grodansparadis/vscp-p1-pulse-interface/images/IMG_20221014_143849.jpg

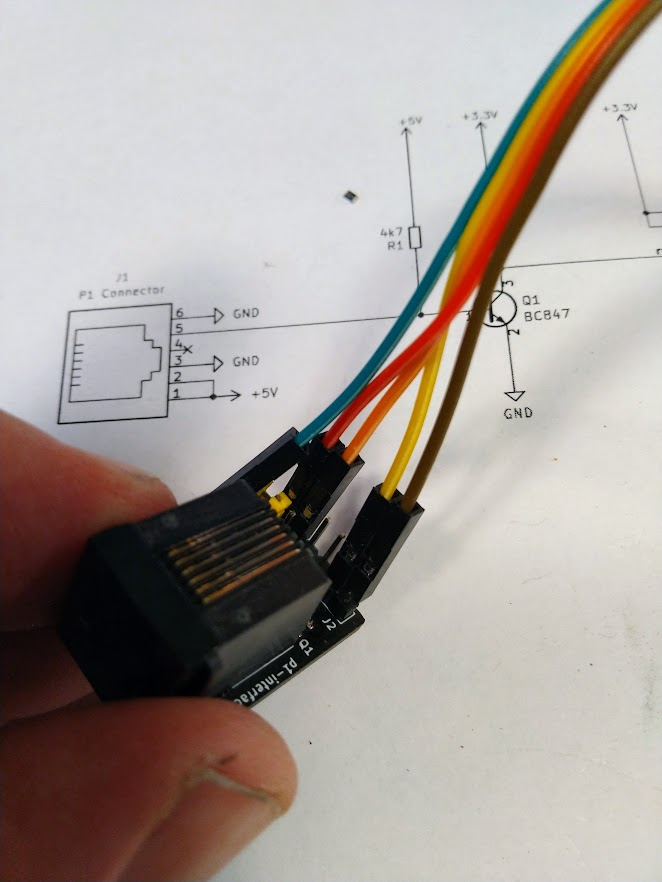
images/IMG_20221014_143849.jpg
