grodansparadis/vscp-p1-pulse-interface/images/IMG_20221014_151402.jpg

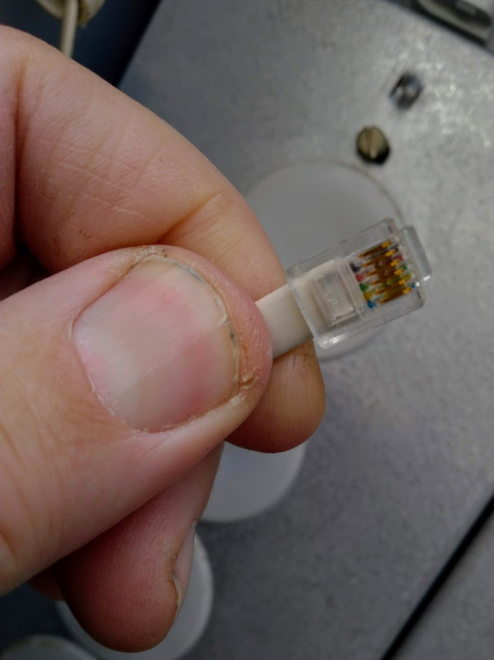
images/IMG_20221014_151402.jpg
