grodansparadis/vscp-p1-pulse-interface/images/IMG_20221014_155922.jpg

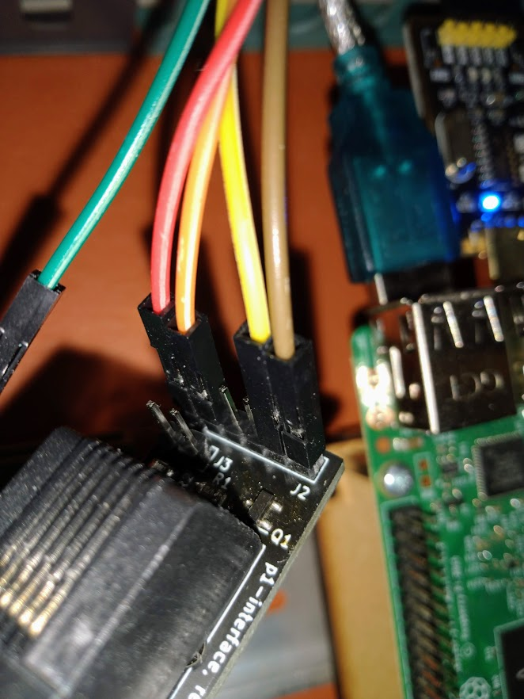
images/IMG_20221014_155922.jpg
