grodansparadis/vscp-p1-pulse-interface/images/IMG_20221020_154316.jpg

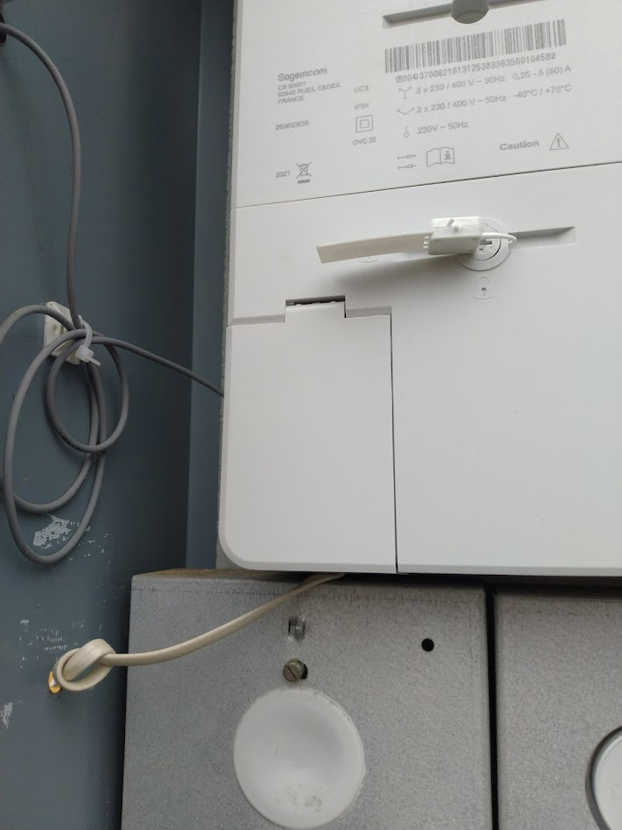
images/IMG_20221020_154316.jpg
