grodansparadis/vscp-p1-pulse-interface/images/IMG_20221020_154810.jpg

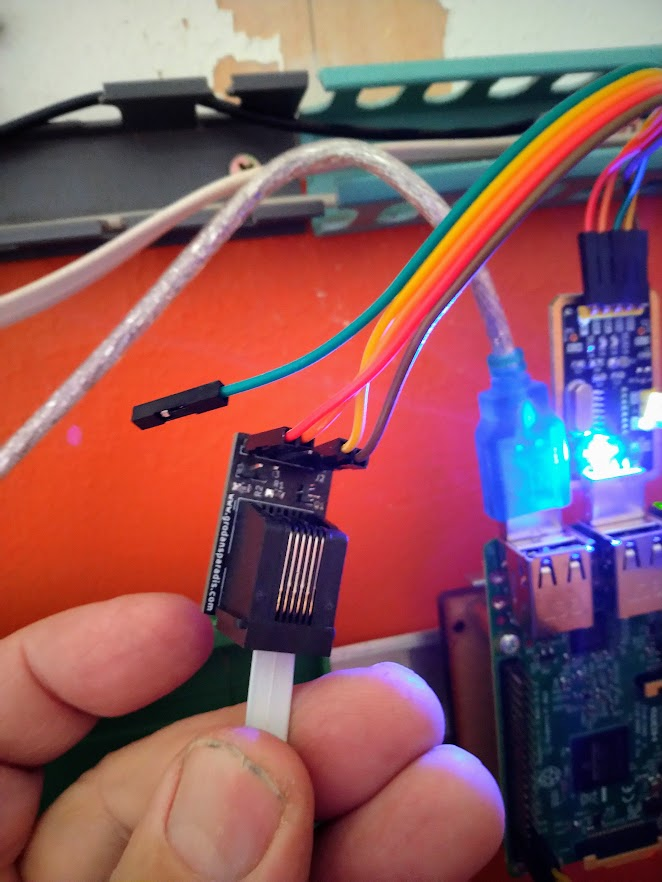
images/IMG_20221020_154810.jpg
