grodansparadis/vscp-p1-pulse-interface/images/schema-rev-a.png

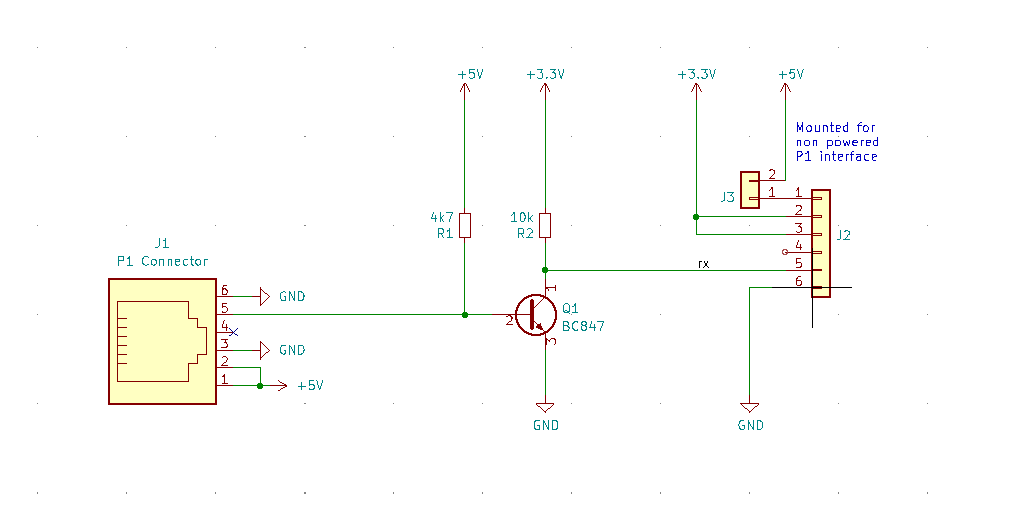
images/schema-rev-a.png
